IMbackK/FluorescentLubricantDetector/IntegratingSphere/FCStd/Straightplate.FCStd

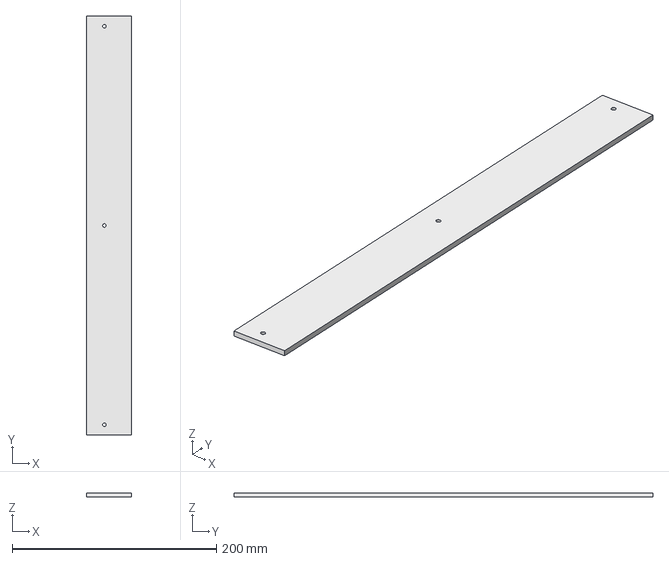
[picture p21: CAD file, 2021-11-20]
IntegratingSphere/FCStd/Straightplate.FCStd
44.0 x 410.0 x 4.00 mm
