IMbackK/FluorescentLubricantDetector/IntegratingSphere/FCStd/CameraMount.FCStd

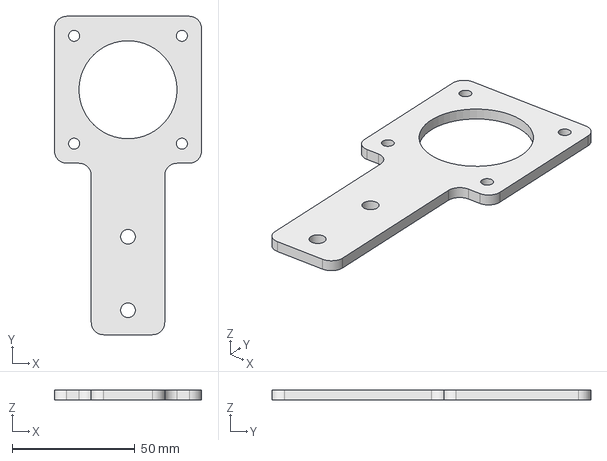
[picture p22: CAD file, 2021-11-20]
IntegratingSphere/FCStd/CameraMount.FCStd
60.0 x 130.0 x 4.00 mm
