IMbackK/FluorescentLubricantDetector/IntegratingSphere/FCStd/ChillPlate.FCStd

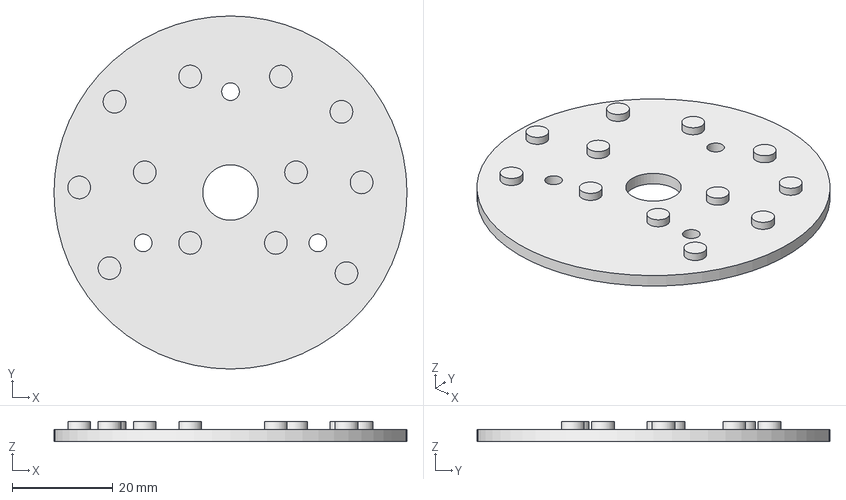
[picture p23: CAD file, 2021-11-20]
IntegratingSphere/FCStd/ChillPlate.FCStd
70.0 x 70.0 x 4.00 mm
