IMbackK/FluorescentLubricantDetector/IntegratingSphere/FCStd/EndPlate.FCStd

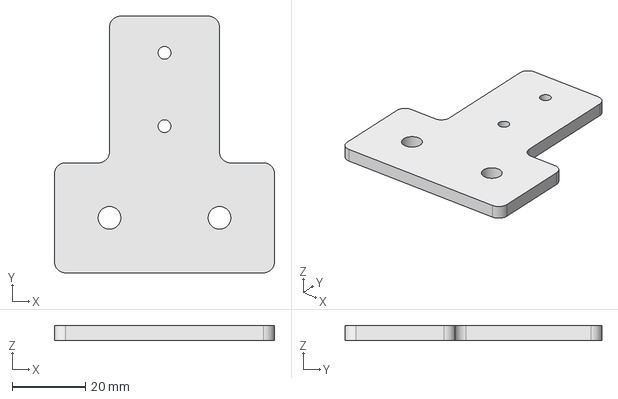
[picture p24: CAD file, 2021-11-20]
IntegratingSphere/FCStd/EndPlate.FCStd
60.0 x 70.0 x 4.00 mm
