IMbackK/FluorescentLubricantDetector/IntegratingSphere/FCStd/HorUpperHolderB.FCStd

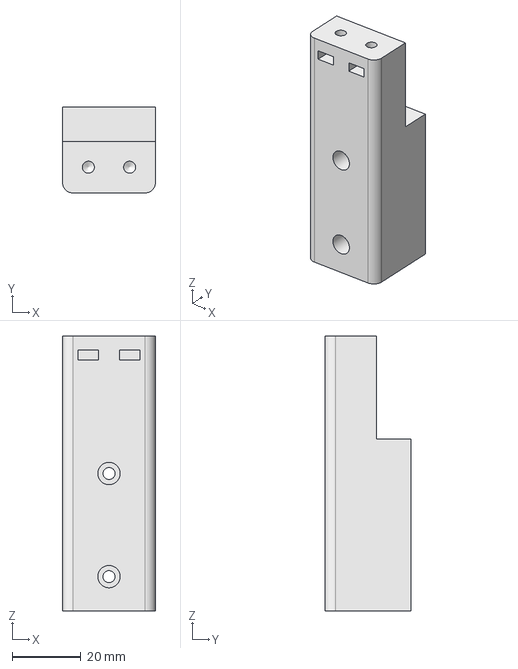
[picture p25: CAD file, 2021-11-20]
IntegratingSphere/FCStd/HorUpperHolderB.FCStd
27.0 x 25.0 x 80.0 mm
