IMbackK/FluorescentLubricantDetector/IntegratingSphere/FCStd/Profile30x60.FCStd

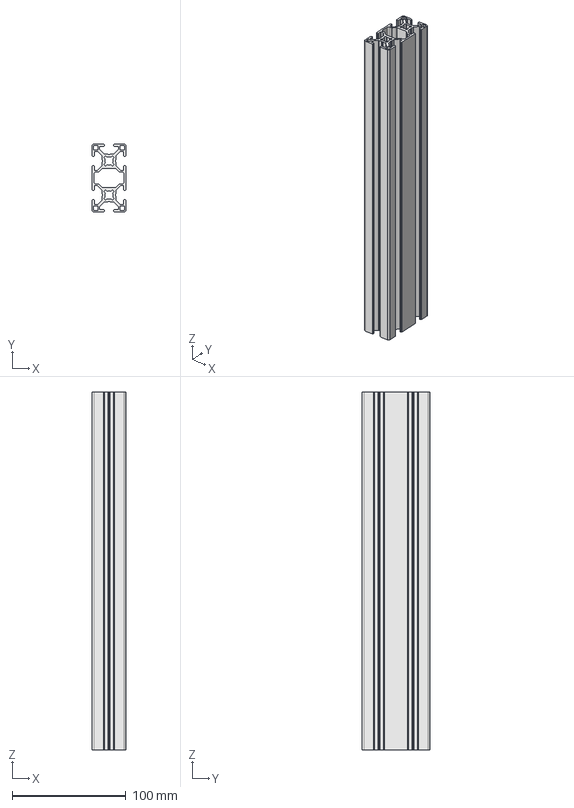
[picture p26: CAD file, 2021-11-20]
IntegratingSphere/FCStd/Profile30x60.FCStd
30.0 x 60.0 x 315.0 mm
