IMbackK/FluorescentLubricantDetector/IntegratingSphere/FCStd/ECaseFloor.FCStd

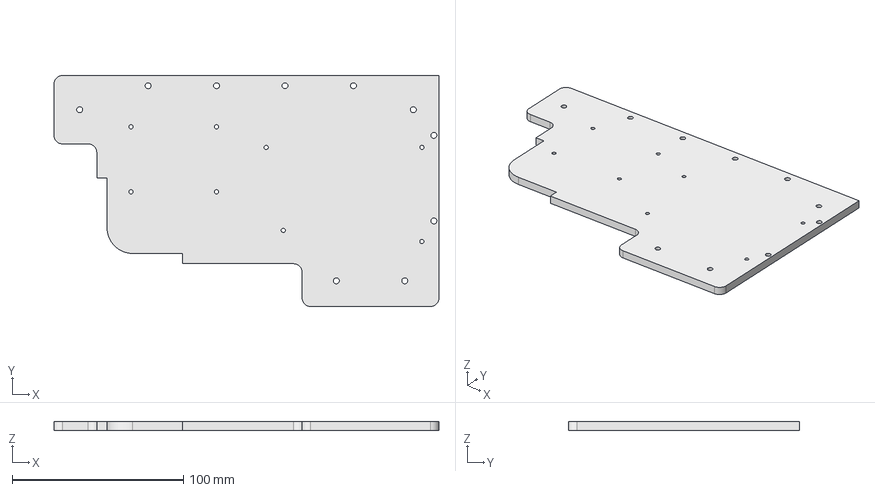
[picture p27: CAD file, 2021-11-20]
IntegratingSphere/FCStd/ECaseFloor.FCStd
225.0 x 135.0 x 5.00 mm
