IMbackK/FluorescentLubricantDetector/IntegratingSphere/FCStd/ECaseRiser.FCStd

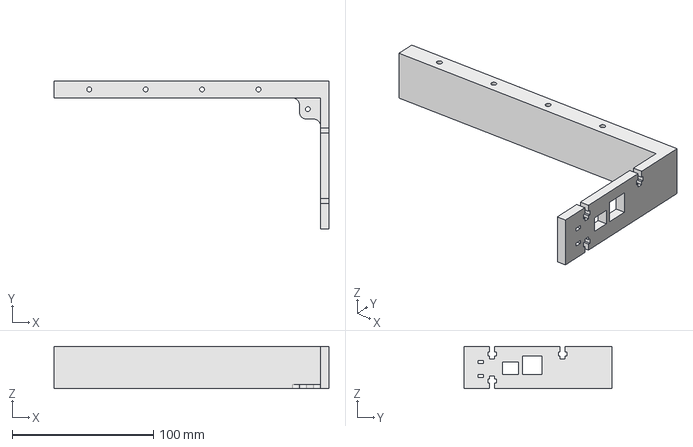
[picture p28: CAD file, 2021-11-20]
IntegratingSphere/FCStd/ECaseRiser.FCStd
195.0 x 105.0 x 30.0 mm
