IMbackK/FluorescentLubricantDetector/IntegratingSphere/FCStd/Post.FCStd

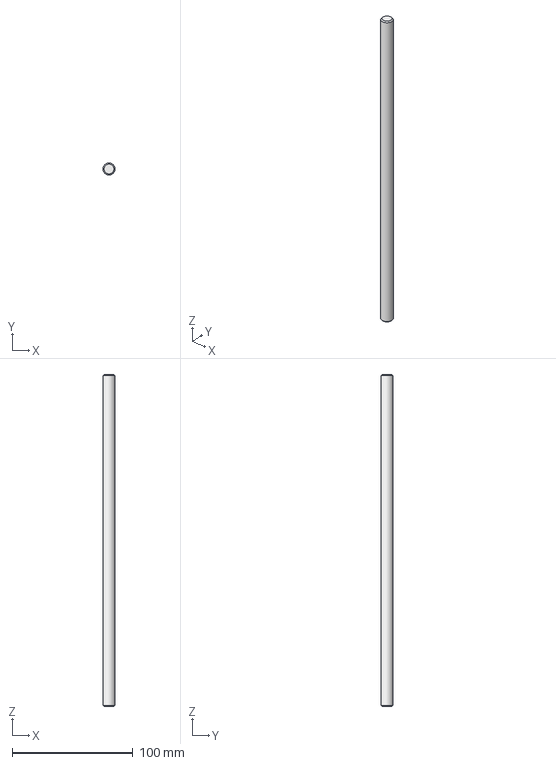
[picture p29: CAD file, 2021-11-20]
IntegratingSphere/FCStd/Post.FCStd
9.99 x 10.00 x 275.0 mm
