IMbackK/FluorescentLubricantDetector/IntegratingSphere/FCStd/RingH.FCStd

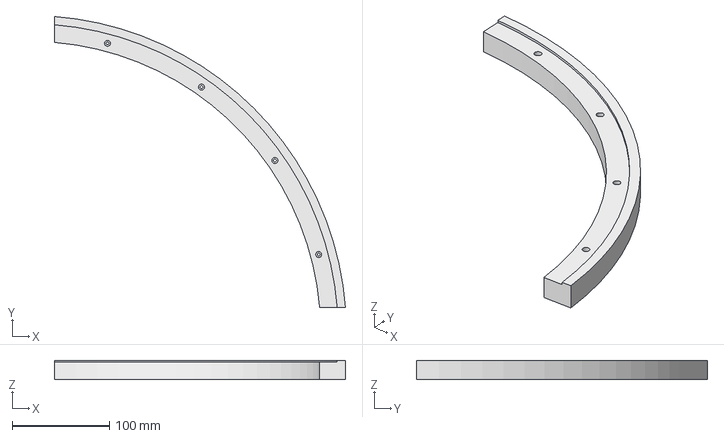
[picture p30: CAD file, 2021-11-20]
IntegratingSphere/FCStd/RingH.FCStd
299.0 x 299.0 x 20.0 mm
