IMbackK/FluorescentLubricantDetector/IntegratingSphere/FCStd/ECaseLID.FCStd

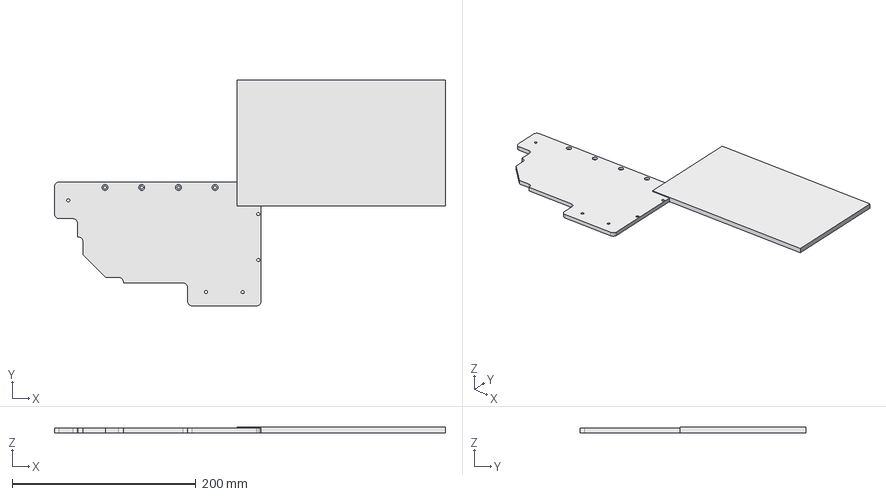
[picture p31: CAD file, 2021-11-20]
IntegratingSphere/FCStd/ECaseLID.FCStd
426.0 x 246.0 x 6.00 mm
Model-Body
Stock
