IMbackK/FluorescentLubricantDetector/IntegratingSphere/FCStd/ChuckStandin.FCStd

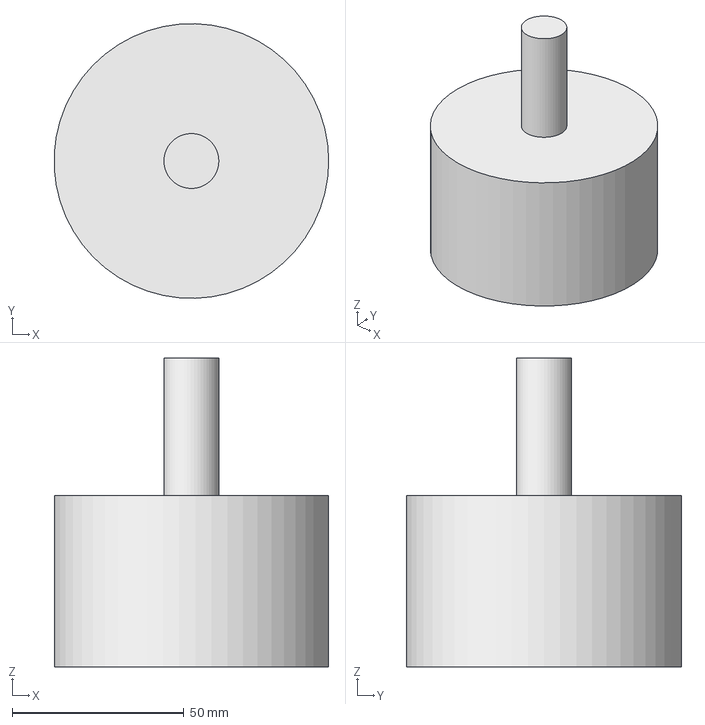
[picture p32: CAD file, 2021-11-20]
IntegratingSphere/FCStd/ChuckStandin.FCStd
79.9 x 80.0 x 90.0 mm
