IMbackK/FluorescentLubricantDetector/IntegratingSphere/FCStd/switchShroud.FCStd

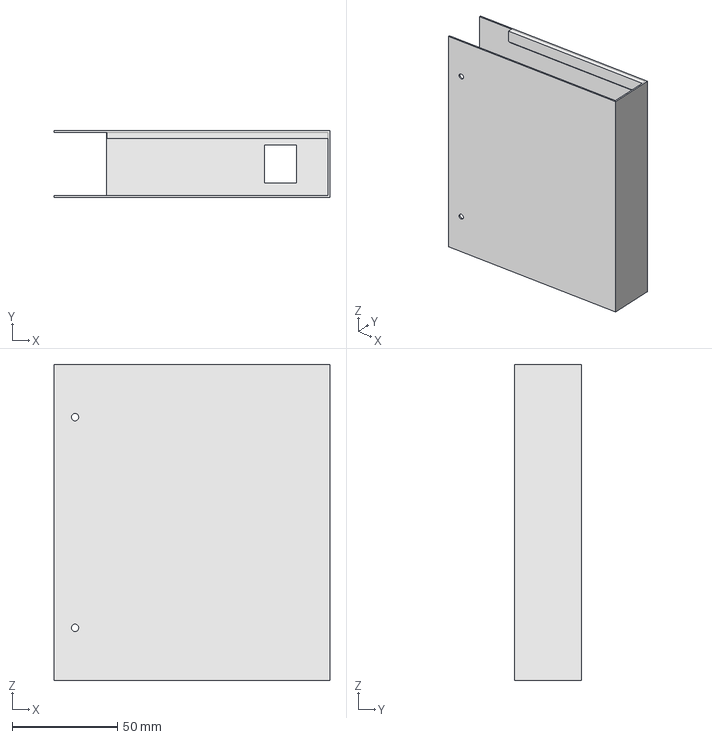
[picture p33: CAD file, 2021-11-20]
IntegratingSphere/FCStd/switchShroud.FCStd
131.0 x 32.0 x 150.0 mm
