IMbackK/FluorescentLubricantDetector/IntegratingSphere/FCStd/CameraStandin.FCStd

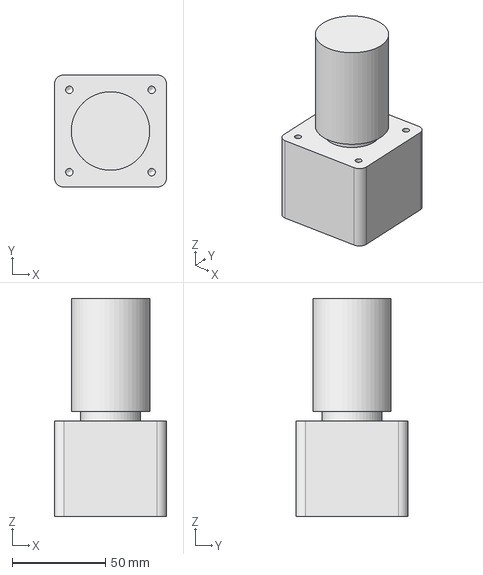
[picture p34: CAD file, 2021-11-20]
IntegratingSphere/FCStd/CameraStandin.FCStd
60.0 x 60.0 x 116.6 mm
