IMbackK/FluorescentLubricantDetector/IntegratingSphere/FCStd/HemBlockA.FCStd

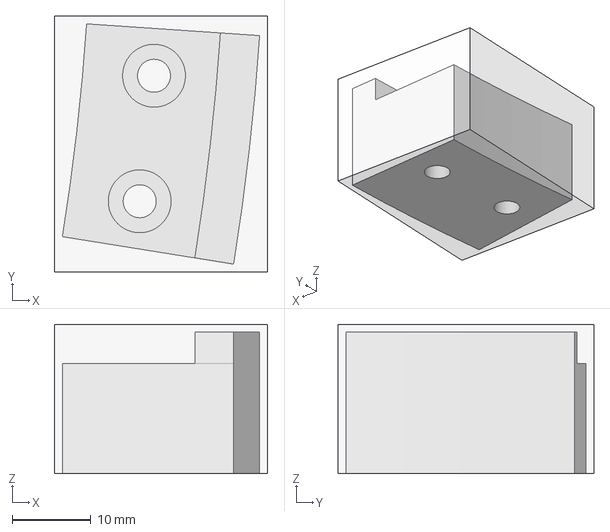
[picture p35: CAD file, 2021-11-20]
IntegratingSphere/FCStd/HemBlockA.FCStd
27.1 x 32.6 x 19.0 mm
Stock
