IMbackK/FluorescentLubricantDetector/IntegratingSphere/FCStd/RingL.FCStd

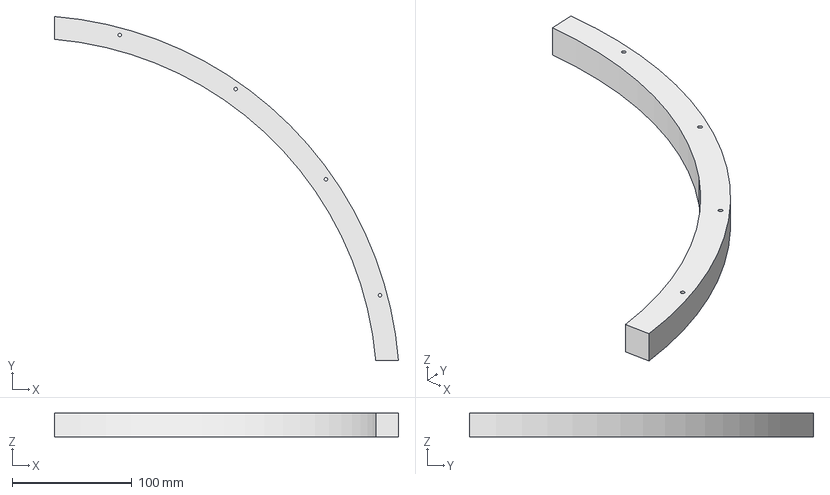
[picture p36: CAD file, 2021-11-20]
IntegratingSphere/FCStd/RingL.FCStd
287.3 x 287.3 x 20.0 mm
