IMbackK/FluorescentLubricantDetector/IntegratingSphere/FCStd/LightMountWedge.FCStd

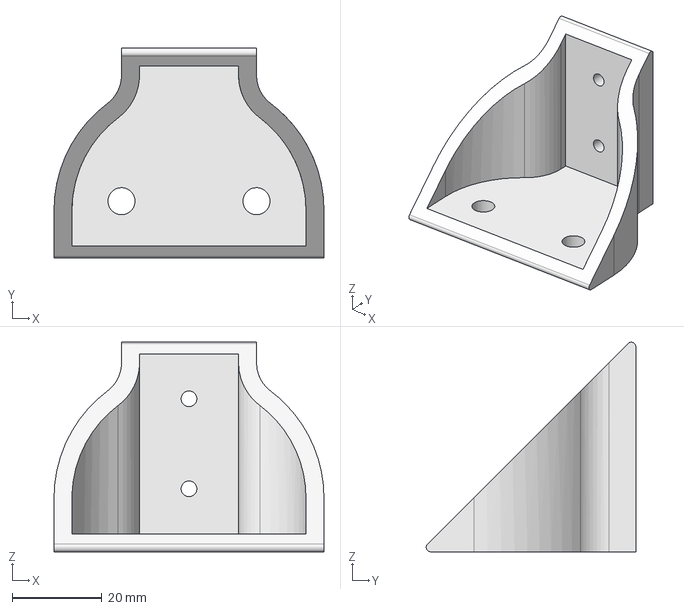
[picture p37: CAD file, 2021-11-20]
IntegratingSphere/FCStd/LightMountWedge.FCStd
60.0 x 46.6 x 46.6 mm
