IMbackK/FluorescentLubricantDetector/IntegratingSphere/FCStd/foot.FCStd

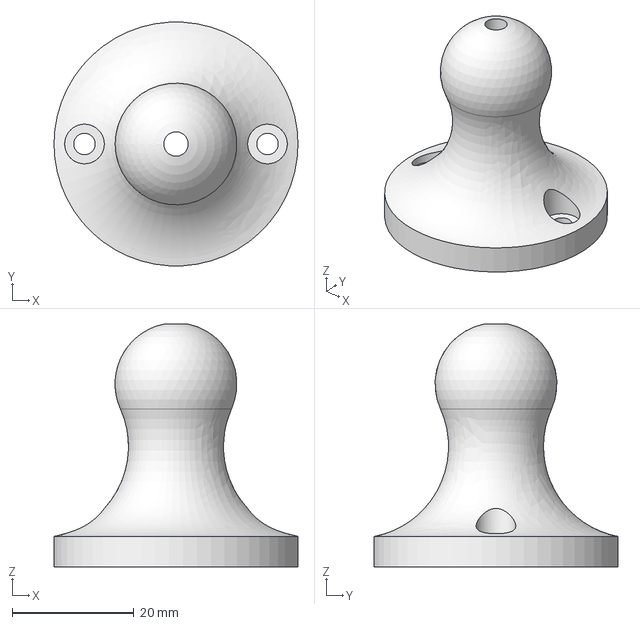
[picture p38: CAD file, 2021-11-20]
IntegratingSphere/FCStd/foot.FCStd
40.0 x 39.9 x 39.8 mm
