IMbackK/FluorescentLubricantDetector/IntegratingSphere/FCStd/itemVert.FCStd

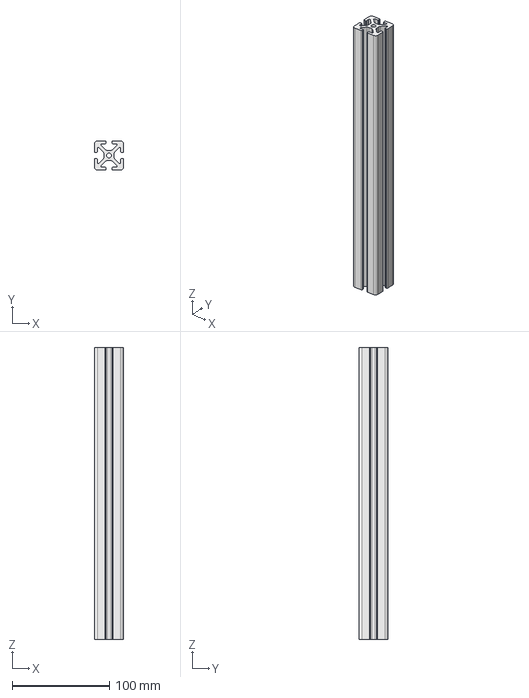
[picture p39: CAD file, 2021-11-20]
IntegratingSphere/FCStd/itemVert.FCStd
30.0 x 30.0 x 300.0 mm
