IMbackK/FluorescentLubricantDetector/IntegratingSphere/FCStd/lenseShroud.FCStd

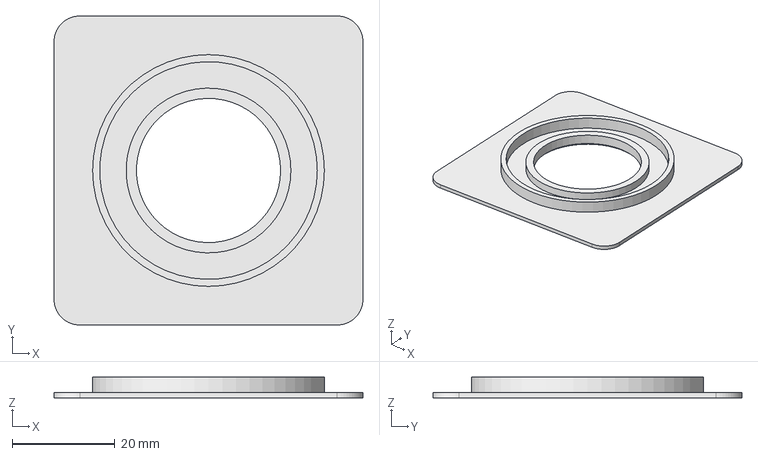
[picture p40: CAD file, 2021-11-20]
IntegratingSphere/FCStd/lenseShroud.FCStd
60.0 x 60.0 x 4.00 mm
