IMbackK/FluorescentLubricantDetector/IntegratingSphere/FCStd/switchBackblock.FCStd

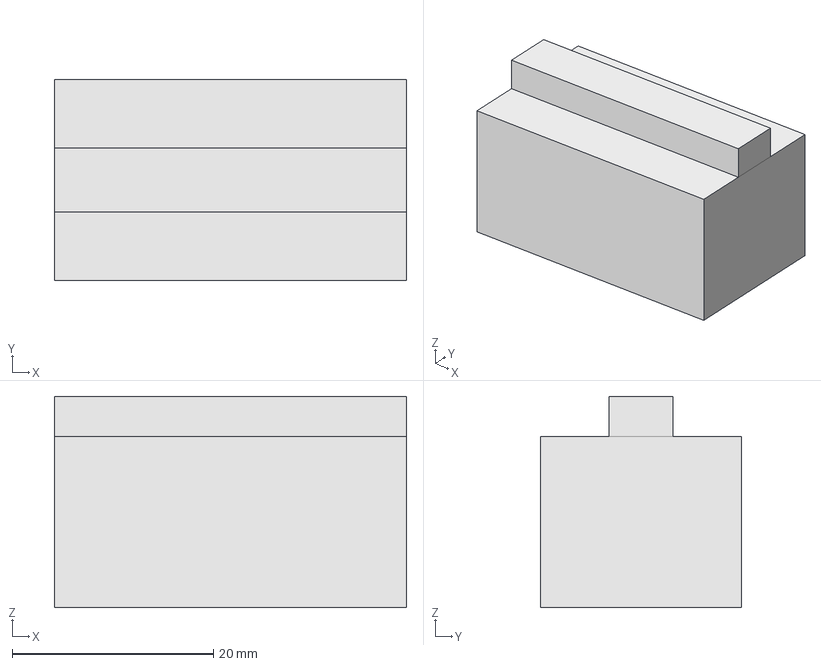
[picture p41: CAD file, 2021-11-20]
IntegratingSphere/FCStd/switchBackblock.FCStd
35.0 x 20.0 x 21.0 mm
