IMbackK/FluorescentLubricantDetector/IntegratingSphere/FCStd/Baffel.FCStd

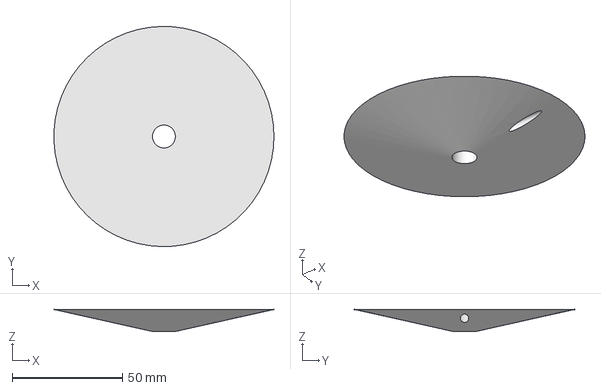
[picture p42: CAD file, 2021-11-20]
IntegratingSphere/FCStd/Baffel.FCStd
99.9 x 100.0 x 10.0 mm
