IMbackK/FluorescentLubricantDetector/IntegratingSphere/FCStd/CameraMountv2.FCStd

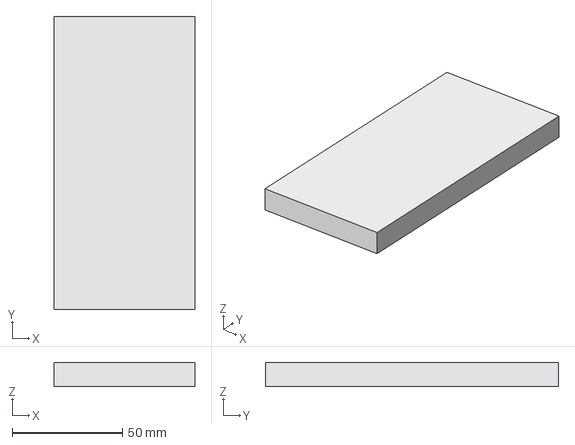
[picture p43: CAD file, 2021-11-20]
IntegratingSphere/FCStd/CameraMountv2.FCStd
64.0 x 133.0 x 11.0 mm
